kiu/apa102nano/pics/apa102nano_full_150x150.jpg

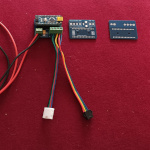
pics/apa102nano_full_150x150.jpg
