kiu/apa102nano/pics/org/IMG_20220424_120357.jpg

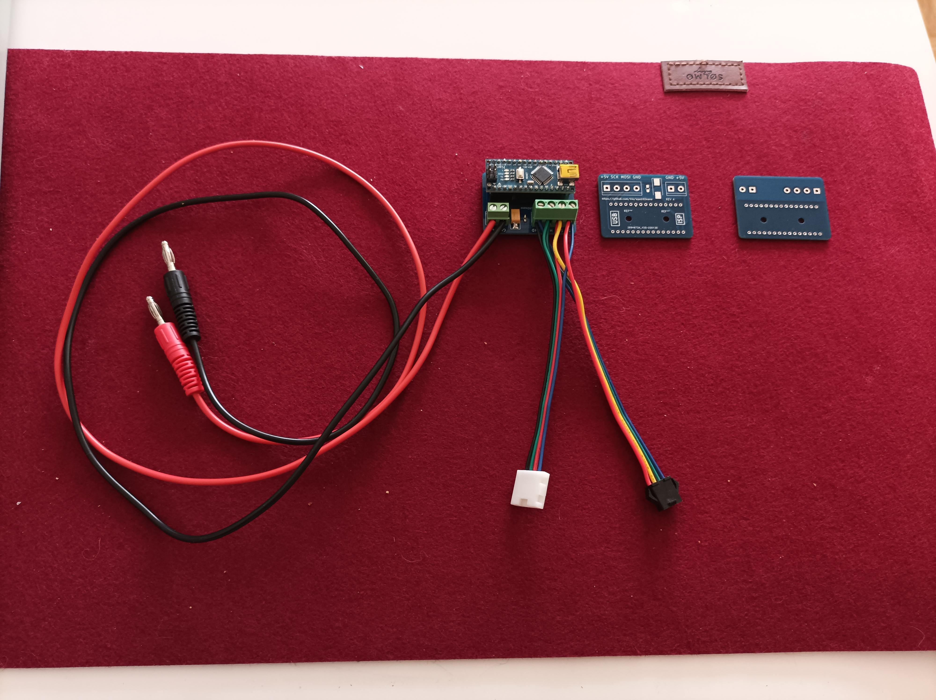
pics/org/IMG_20220424_120357.jpg
