kiu/apa102nano/pics/org/IMG_20220424_120618.jpg

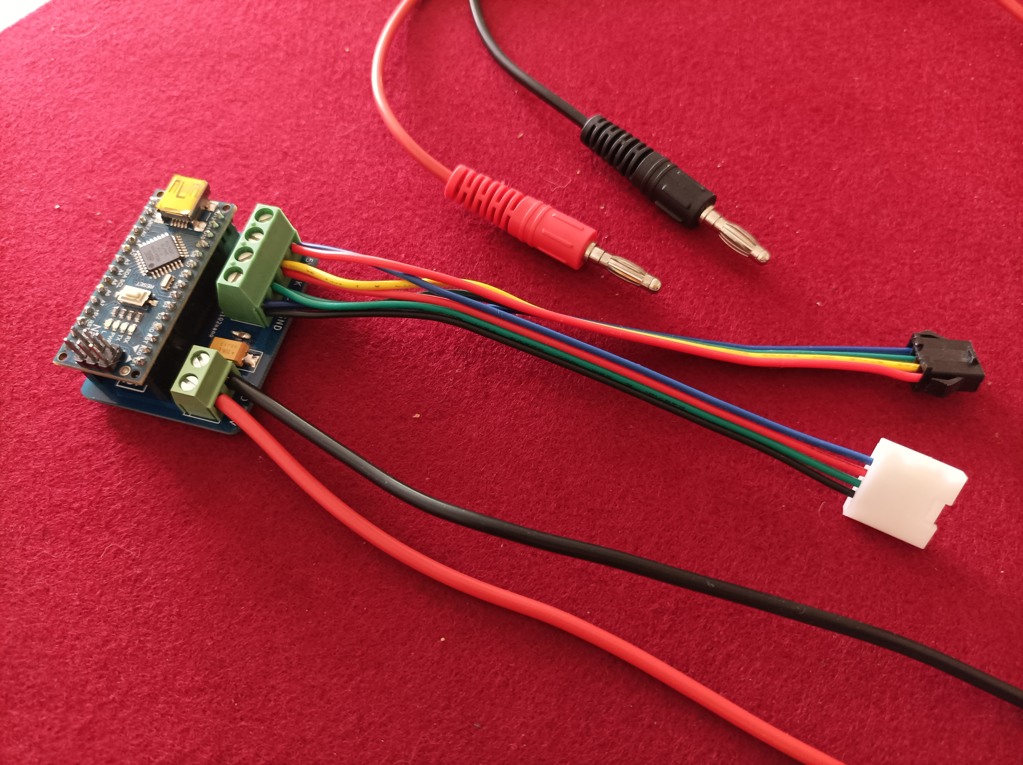
pics/org/IMG_20220424_120618.jpg
